ZeusyBoy98/ZBoard-V1/IMG/pcb.png

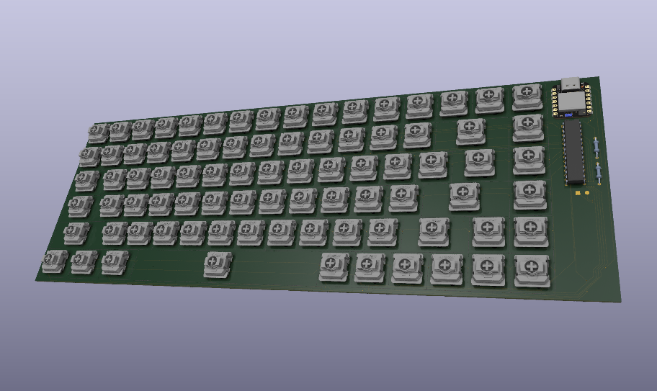
IMG/pcb.png
