ZeusyBoy98/ZBoard-V1/CAD/Keycaps/Keycap-2u.step

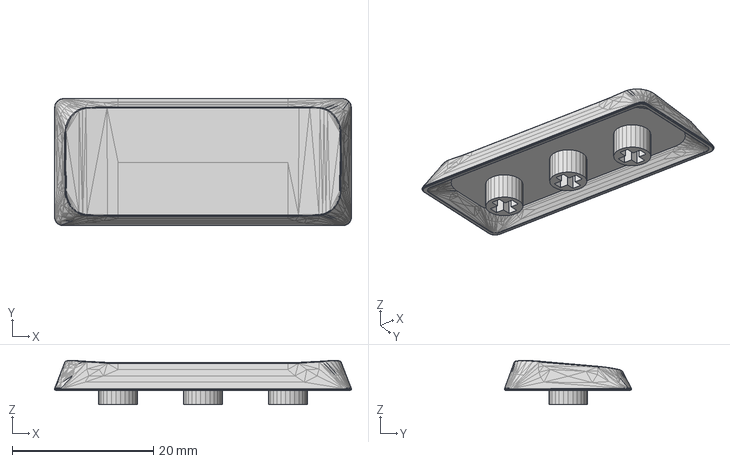
[picture p25: CAD file, 2026-04-03]
CAD/Keycaps/Keycap-2u.step
42.0 x 18.0 x 6.23 mm
