ZeusyBoy98/ZBoard-V1/CAD/ZBoard-V1-Full.stp

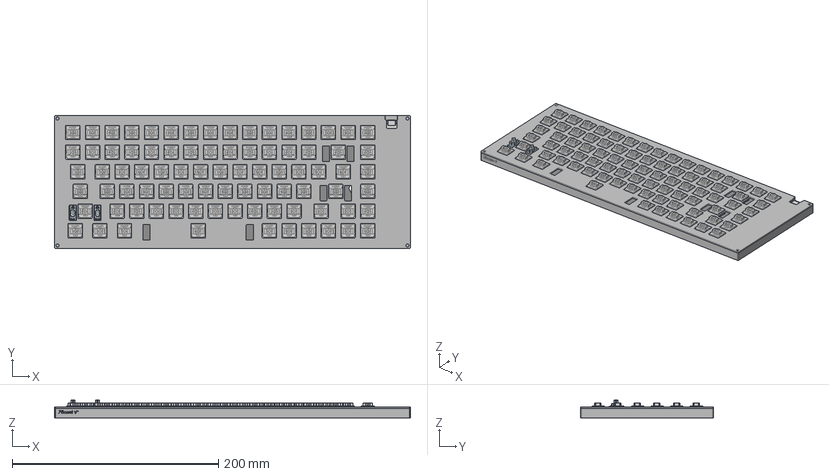
[picture p26: CAD file, 2026-06-06, an earlier design]
CAD/ZBoard-V1-Full.stp
345.0 x 129.0 x 17.0 mm
