ZeusyBoy98/ZBoard-V1/IMG/Journal/0304.png

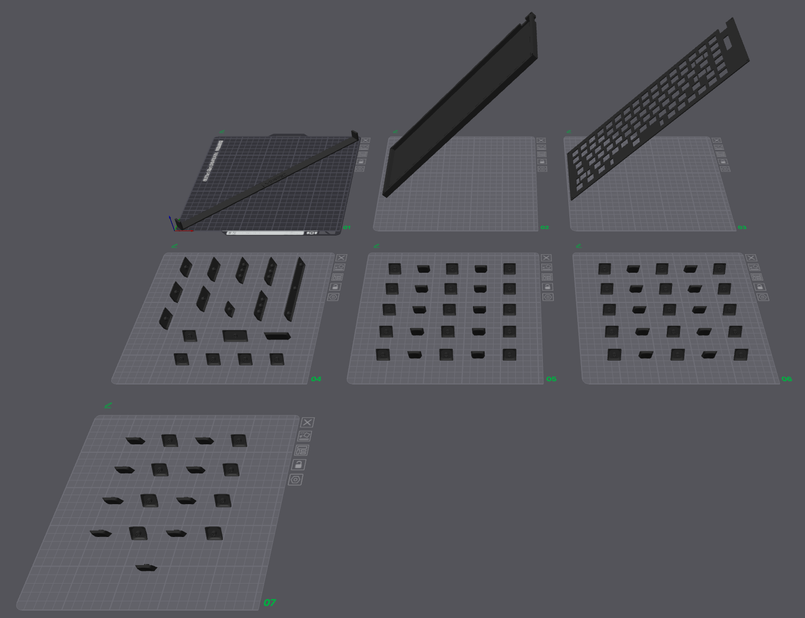
IMG/Journal/0304.png
