ZeusyBoy98/ZBoard-V1/IMG/Journal/1703.png

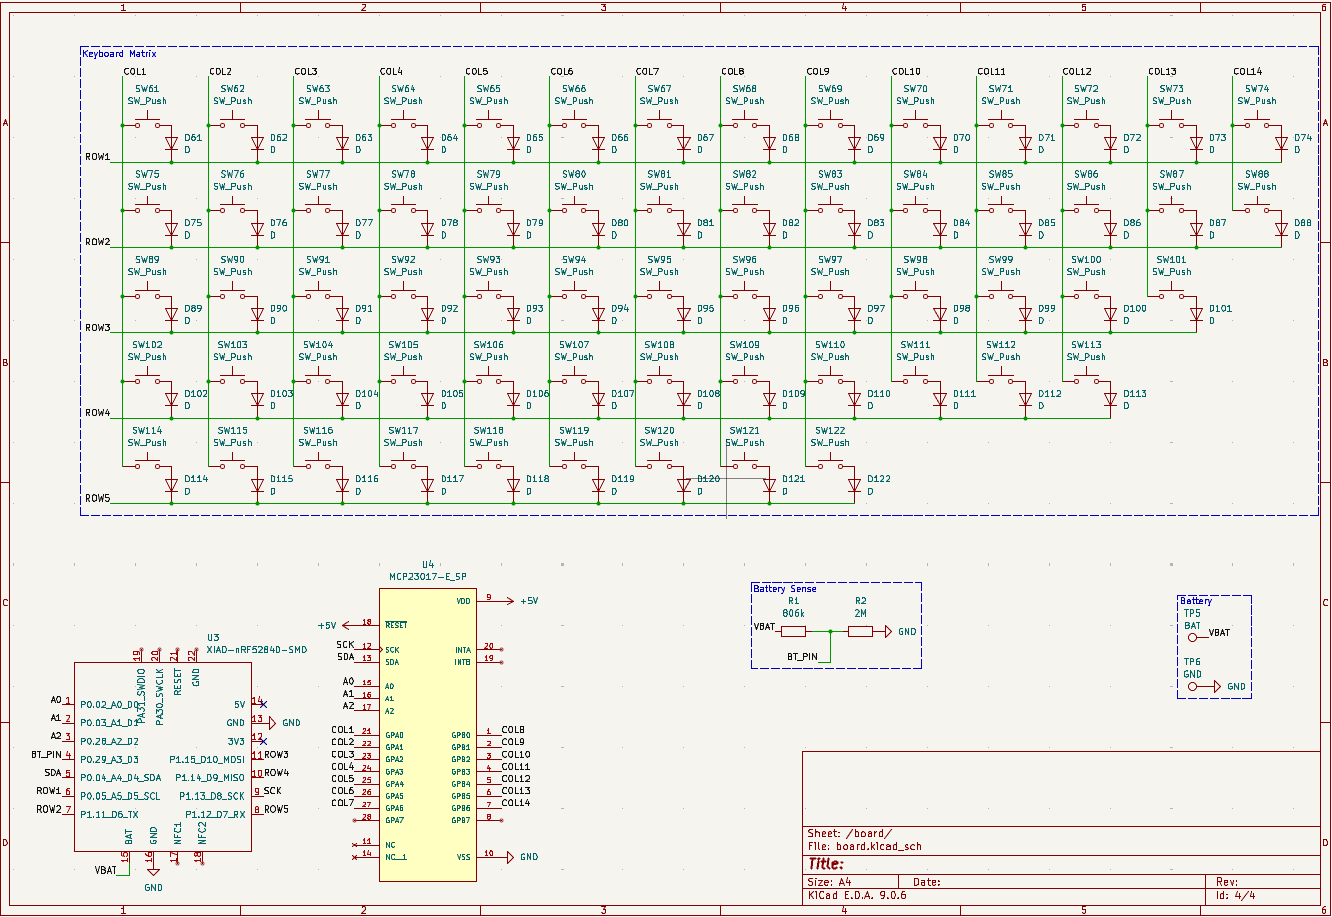
IMG/Journal/1703.png
