ZeusyBoy98/ZBoard-V1/IMG/Journal/1903.png

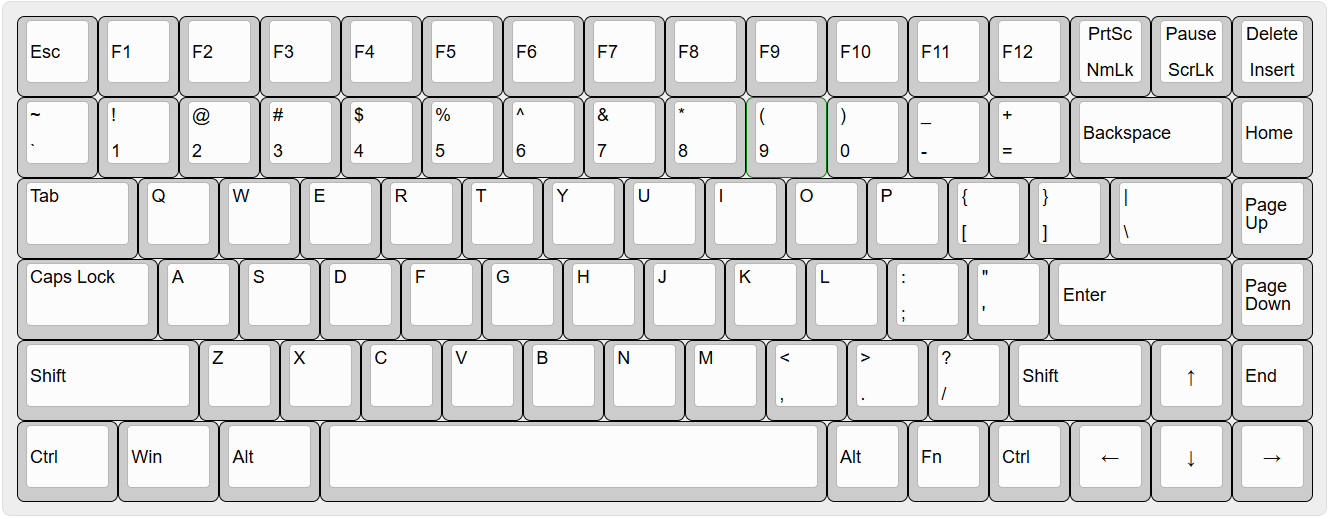
IMG/Journal/1903.png
