ZeusyBoy98/ZBoard-V1/IMG/Journal/2203.png

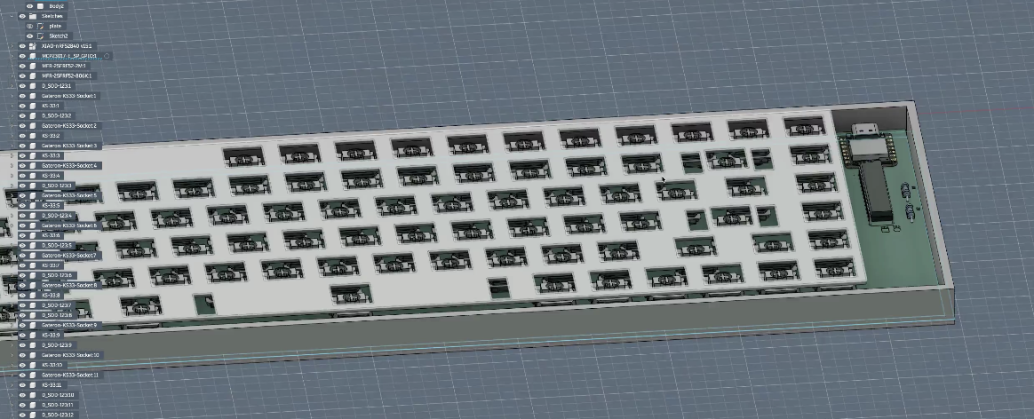
IMG/Journal/2203.png
