ZeusyBoy98/ZBoard-V1/IMG/Journal/2803.png

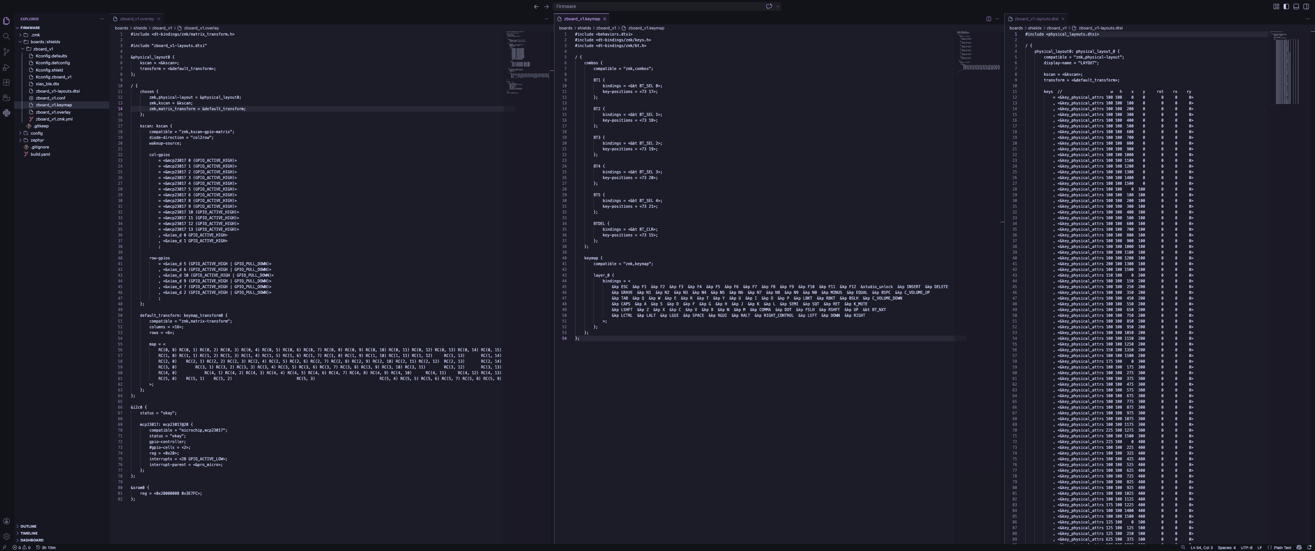
IMG/Journal/2803.png
