ZeusyBoy98/ZBoard-V1/IMG/Journal/3103.png

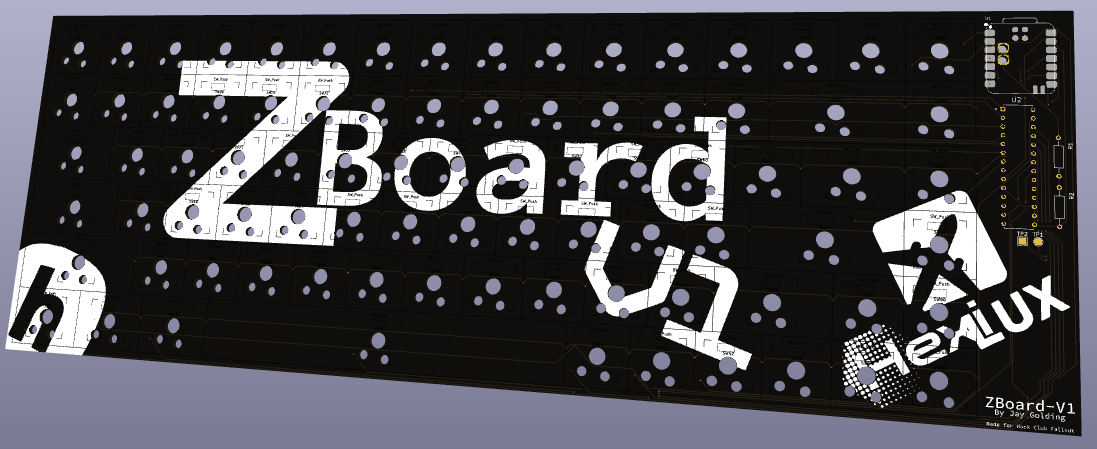
IMG/Journal/3103.png
