ZeusyBoy98/ZBoard-V1/IMG/Journal/28032.png

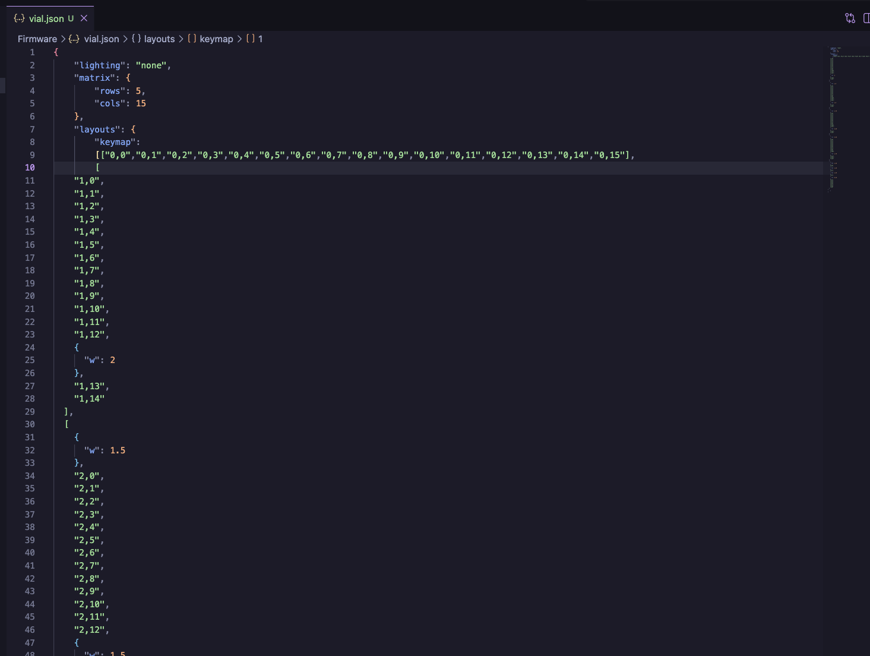
IMG/Journal/28032.png
