ZeusyBoy98/ZBoard-V1/IMG/Journal/31032.png

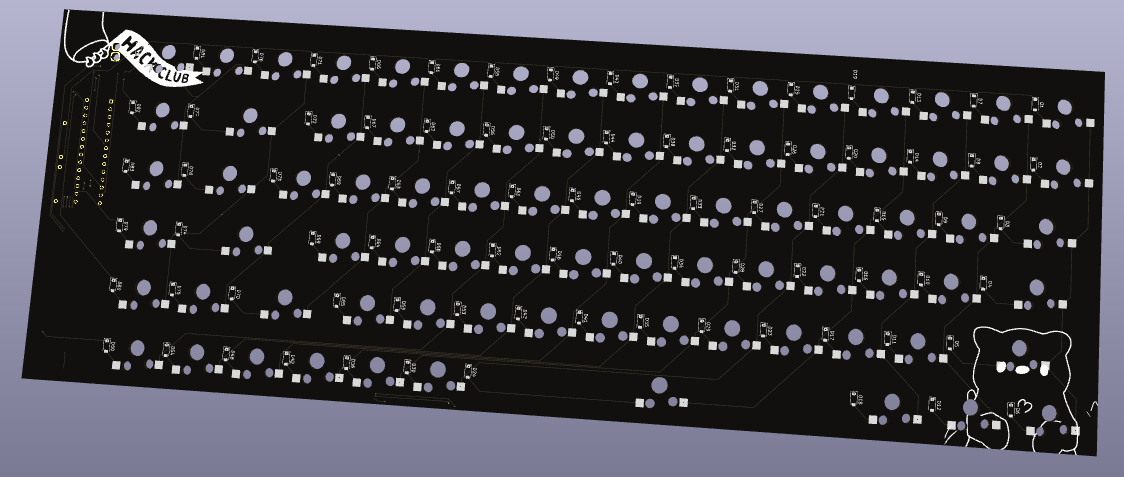
IMG/Journal/31032.png
